ayoo5/audionote/docs/08-assets/demo-photos/Development Stage with Laptop.jpeg

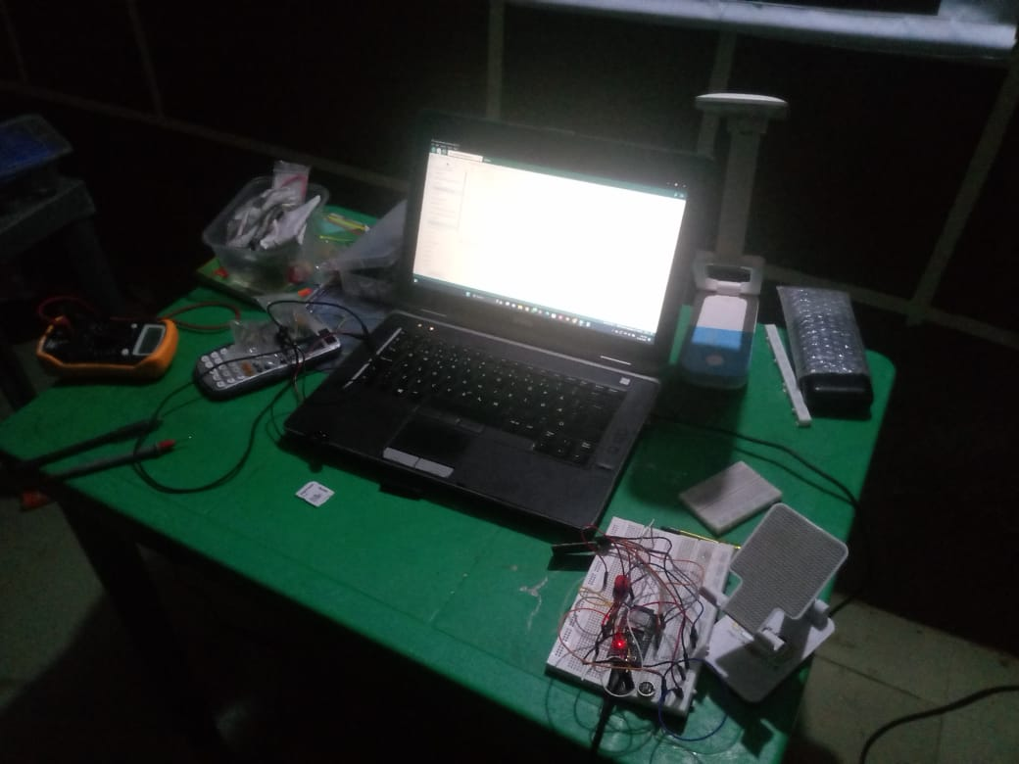
docs/08-assets/demo-photos/Development Stage with Laptop.jpeg
