ayoo5/audionote/docs/08-assets/demo-photos/Top View 2.jpeg

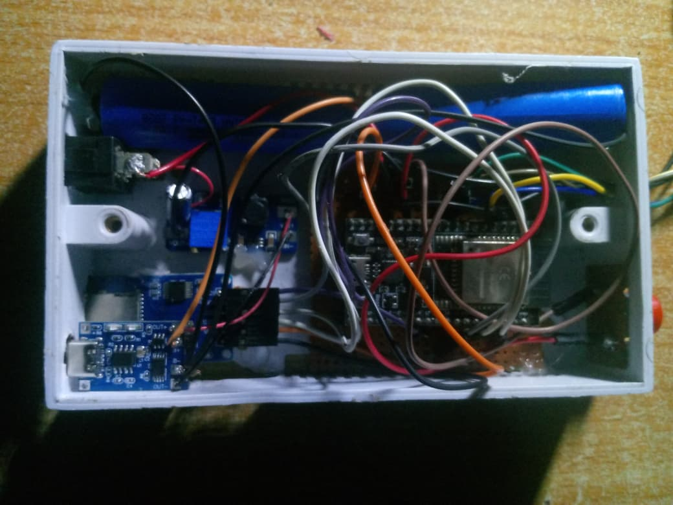
docs/08-assets/demo-photos/Top View 2.jpeg
