ayoo5/audionote/docs/08-assets/demo-photos/Top View 3.jpeg

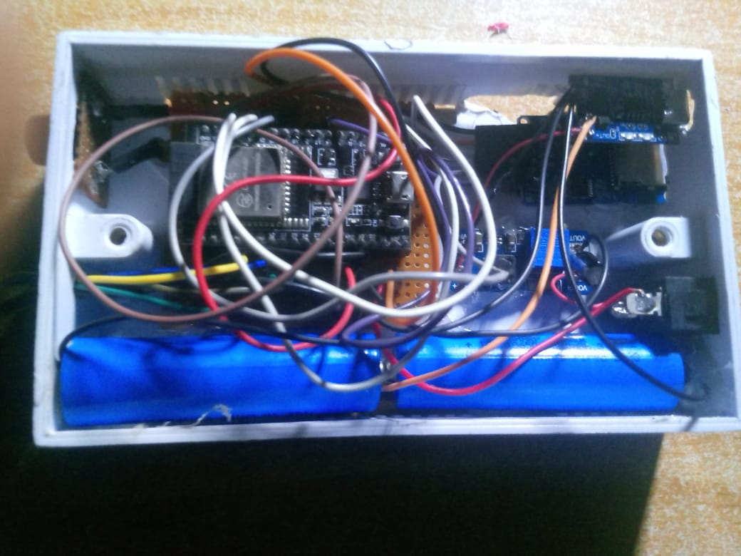
docs/08-assets/demo-photos/Top View 3.jpeg
