ayoo5/audionote/docs/08-assets/diagrams/Correct audio wave for silence.png

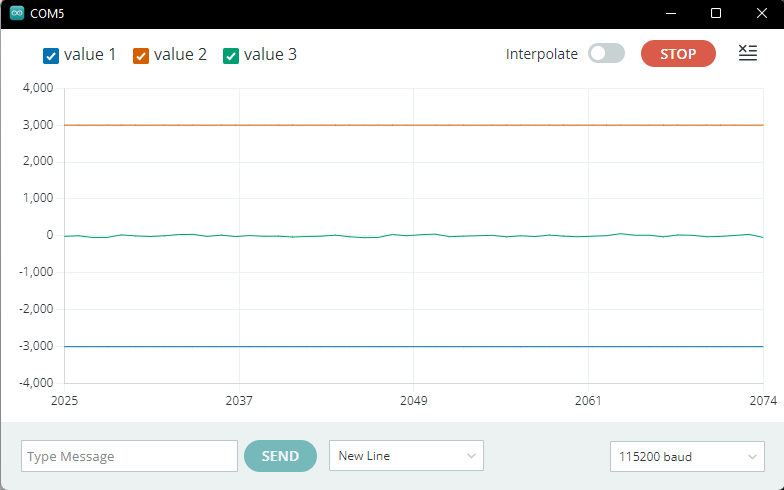
docs/08-assets/diagrams/Correct audio wave for silence.png
