ayoo5/audionote/hardware/enclosure/Bottom View.jpg

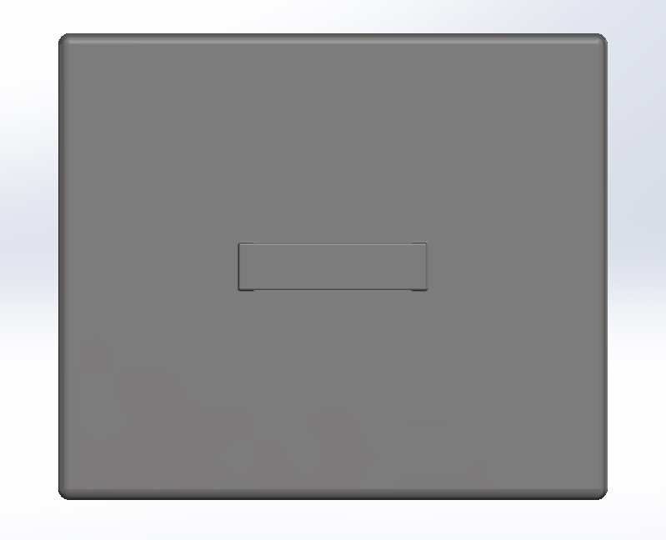
hardware/enclosure/Bottom View.jpg
