ayoo5/audionote/hardware/enclosure/Right View.jpg

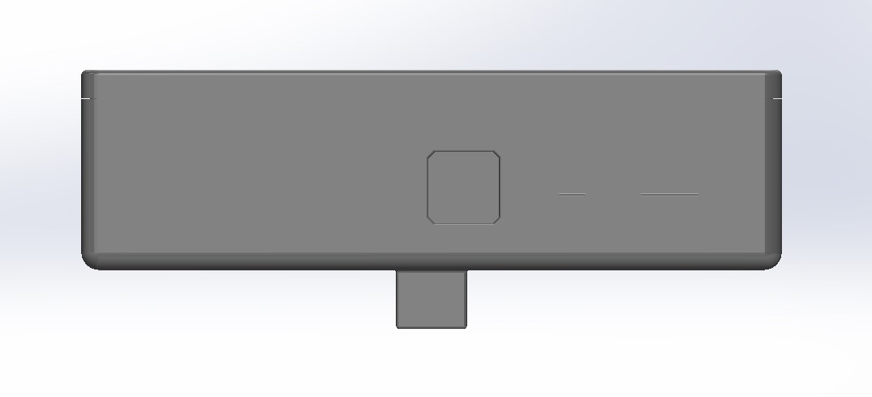
hardware/enclosure/Right View.jpg
