ayoo5/audionote/hardware/enclosure/Screenshot 2025-12-20 192914.jpg

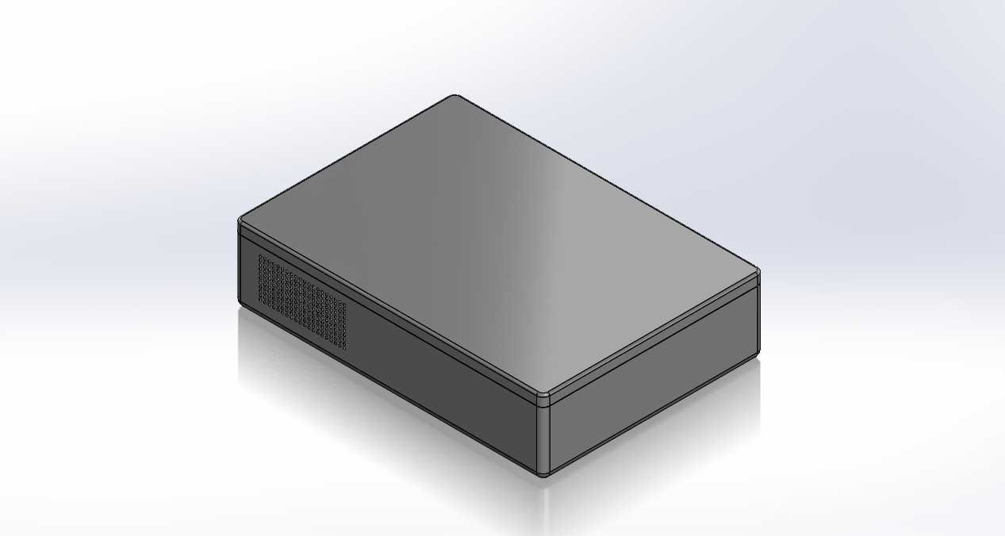
hardware/enclosure/Screenshot 2025-12-20 192914.jpg
