ayoo5/audionote/hardware/enclosure/Screenshot 2025-12-20 234932.jpg

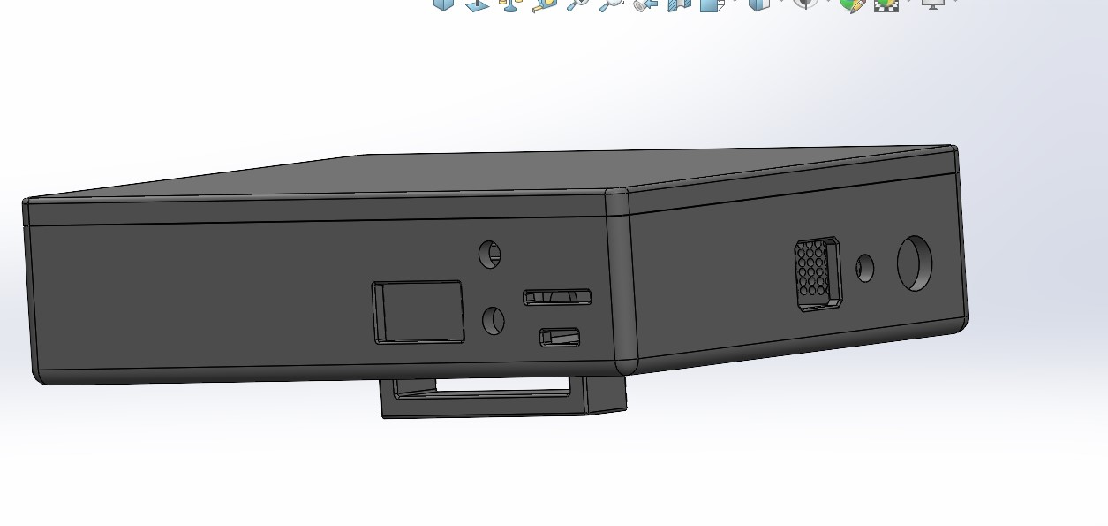
hardware/enclosure/Screenshot 2025-12-20 234932.jpg
