ayoo5/audionote/hardware/enclosure/Side view 2.jpg

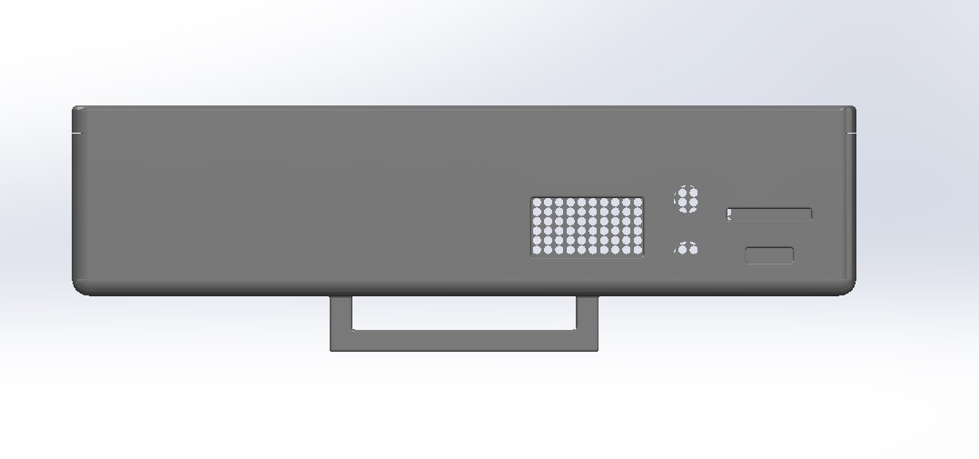
hardware/enclosure/Side view 2.jpg
