ayoo5/audionote/hardware/enclosure/Side view.jpg

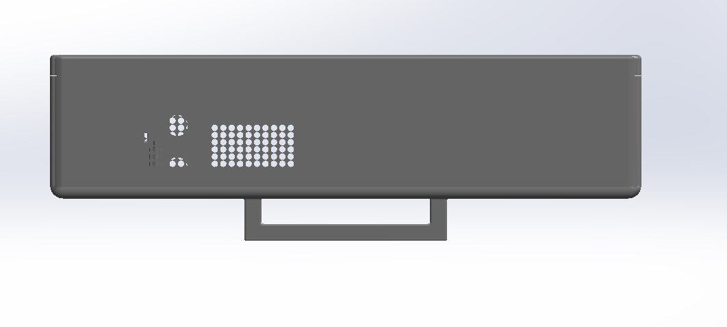
hardware/enclosure/Side view.jpg
