ayoo5/audionote/hardware/enclosure/Top View.jpg

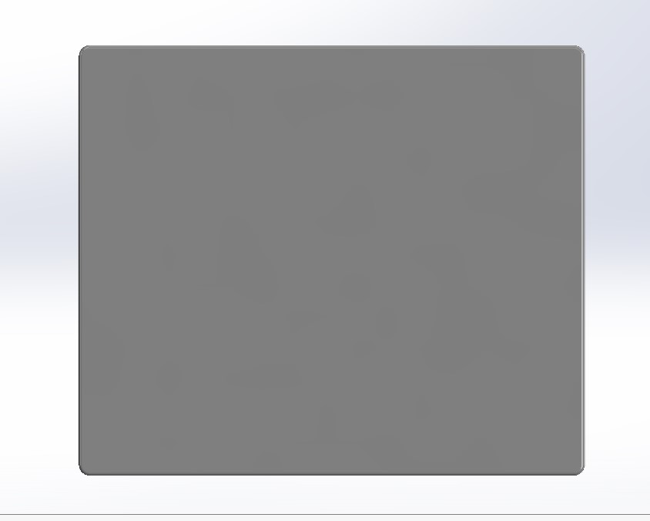
hardware/enclosure/Top View.jpg
