ayoo5/audionote/docs/08-assets/components/glue gun.jpg

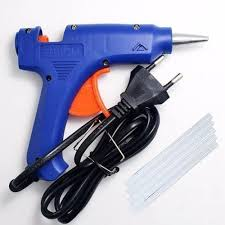
docs/08-assets/components/glue gun.jpg
