ayoo5/audionote/docs/08-assets/components/soldering iron.jpg

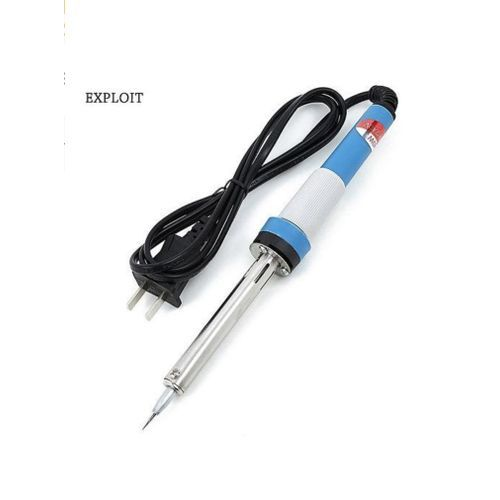
docs/08-assets/components/soldering iron.jpg
