ayoo5/audionote/hardware/enclosure/Assembly.JPG

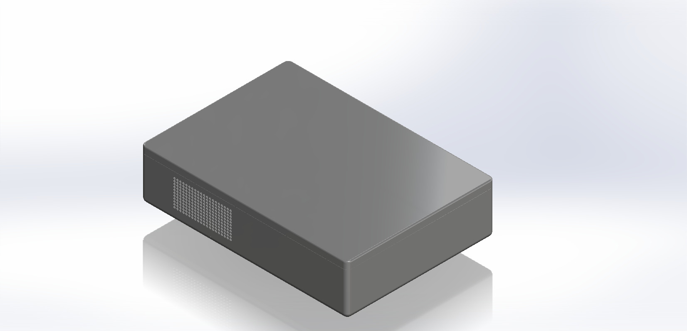
hardware/enclosure/Assembly.JPG
